hggh/window-contact-bme280-rfm69/src/config.example.h

#define NODEID        101
#define NETWORKID     100
#define GATEWAYID     1
#define FREQUENCY     RF69_433MHZ
#define ENCRYPTKEY    "sampleEncryptKey"
#define DEBUG 1

/*
 * 1 = handle is left
 * 2 = handle is right
*/
#define WINDOW_ORIENTATION 1
